Makerfabs/MaTouch-ESP32-S3-Rotary-IPS-Display-with-Touch-2.1-ST7701/example/fs_test/data/2.jpg

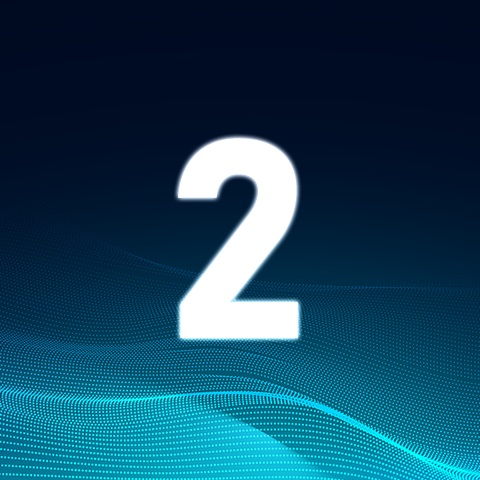
example/fs_test/data/2.jpg
